Noahnc/grafana-coffee-counter/include/certificates.h

#ifndef certificates_h
#define certificates_h

/*
 * USERTrust RSA Certification Authority
 * root CA used for Grafana certificates.
 */

static const char grafanaCert[] = R"EOF(
-----BEGIN CERTIFICATE-----
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
MrY=
-----END CERTIFICATE-----
)EOF";

#endif
